TinyCircuits/TinyCircuits-Whisker-IR-Heat-Camera-AST1045/images/AST1045-Tutorial-Animation-02.gif

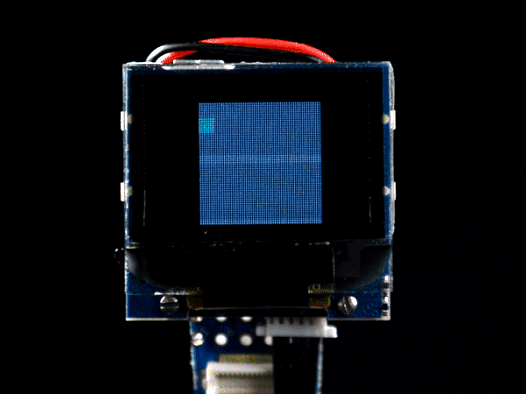
images/AST1045-Tutorial-Animation-02.gif
